DarkJaeger/open-keg-scale/open_keg_scale/3d printer files/images/00d7e51b-67e7-4740-b3d5-3baff1cd7baa.png

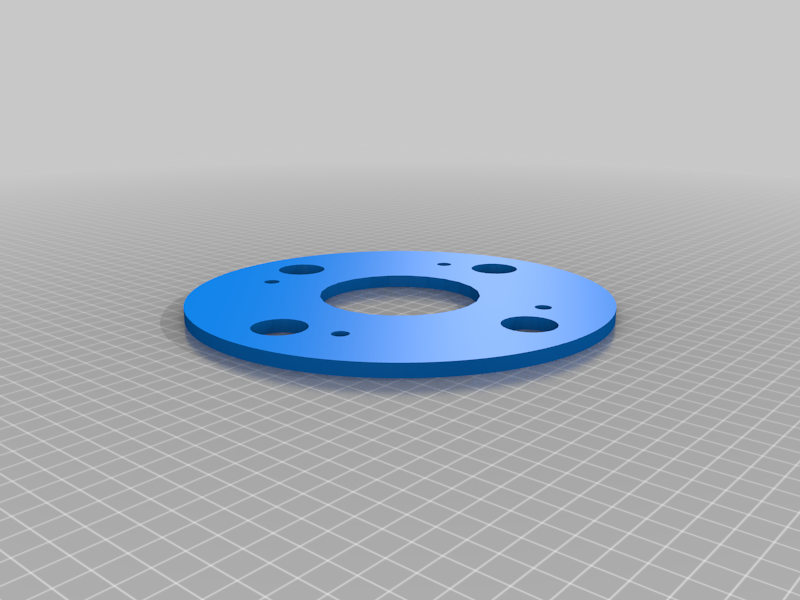
open_keg_scale/3d printer files/images/00d7e51b-67e7-4740-b3d5-3baff1cd7baa.png
