DarkJaeger/open-keg-scale/open_keg_scale/3d printer files/images/8a149a91-782a-4f04-a723-3c5b08f16a64.png

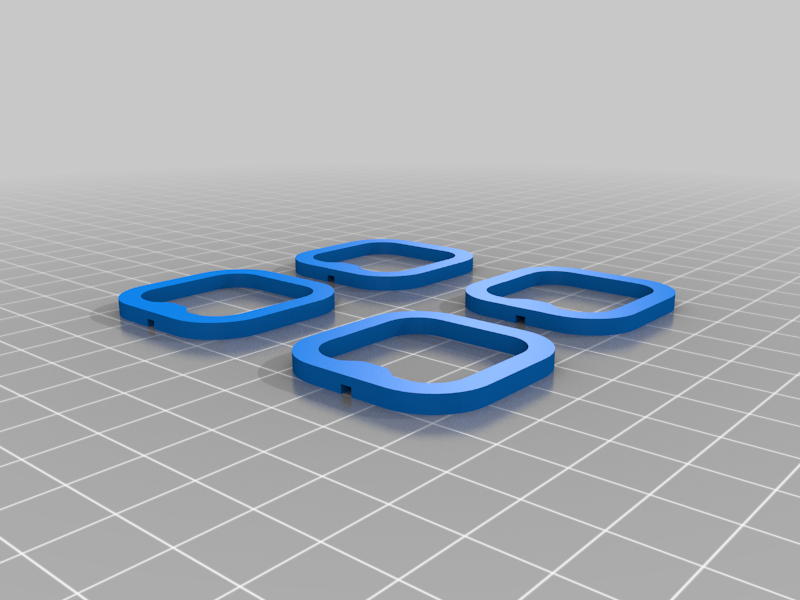
open_keg_scale/3d printer files/images/8a149a91-782a-4f04-a723-3c5b08f16a64.png
