DarkJaeger/open-keg-scale/open_keg_scale/3d printer files/images/6375c254-c555-41b0-b193-8b373e29b0f3.png

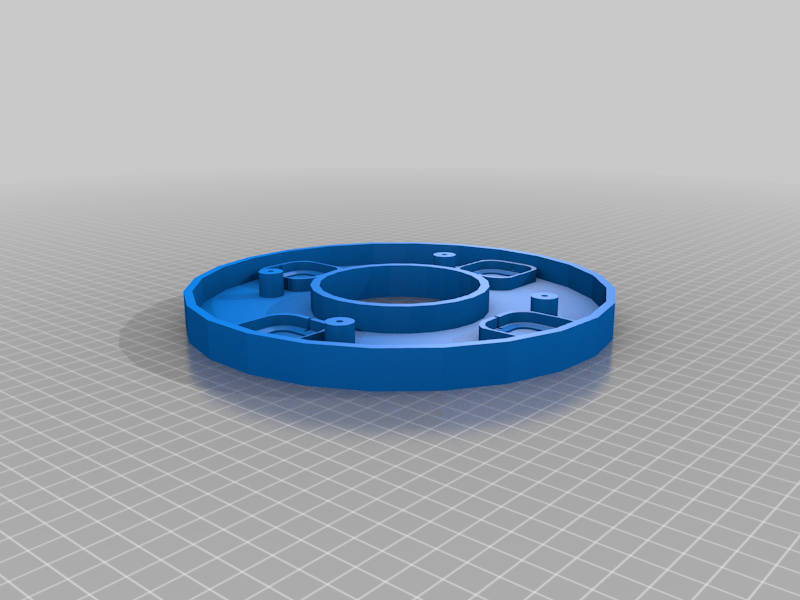
open_keg_scale/3d printer files/images/6375c254-c555-41b0-b193-8b373e29b0f3.png
