DarkJaeger/open-keg-scale/open_keg_scale/Wiring info.jpg

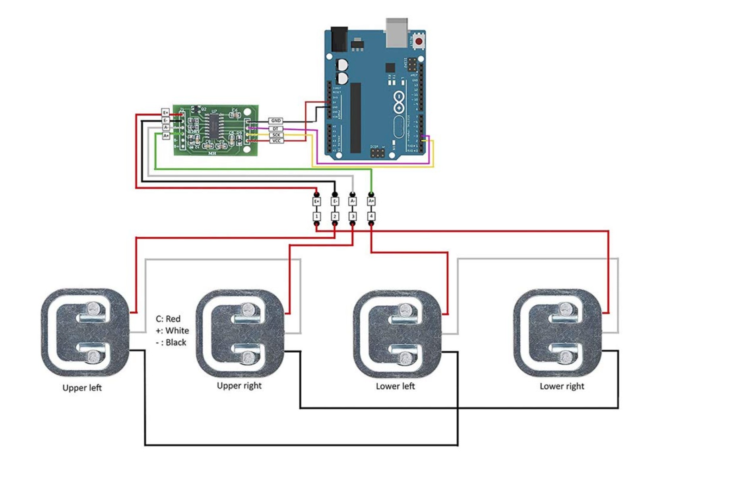
open_keg_scale/Wiring info.jpg
